ADDTDR/Pitanga/Hardware_Kicad/ltp_kikad_b.png

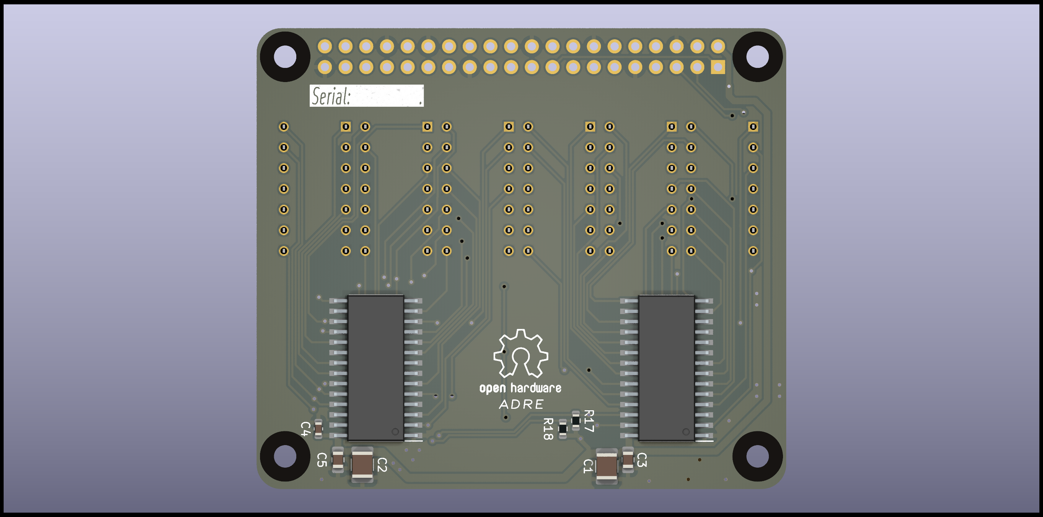
Hardware_Kicad/ltp_kikad_b.png
