ADDTDR/Pitanga/Hardware_Kicad/ltp_kikad_f.png

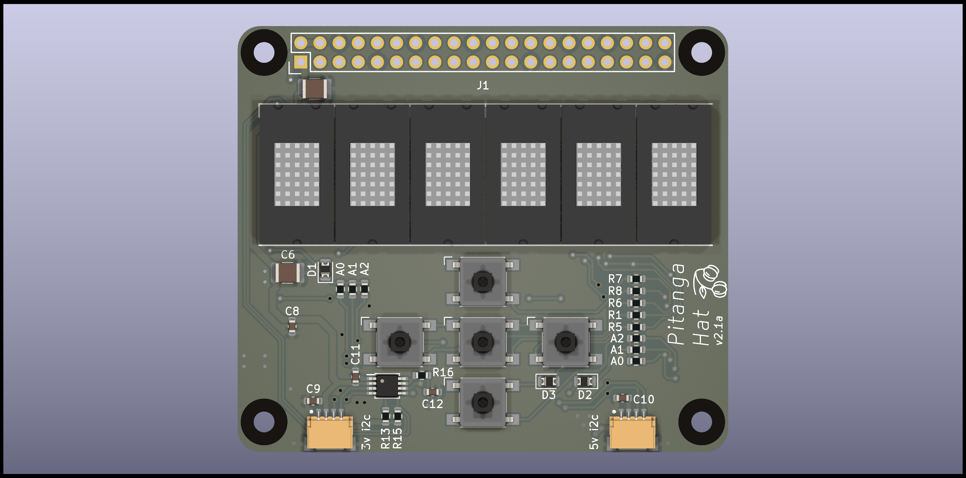
Hardware_Kicad/ltp_kikad_f.png
