ADDTDR/Pitanga/Hardware_Kicad/render_images/ltp_05_f_kikad.png

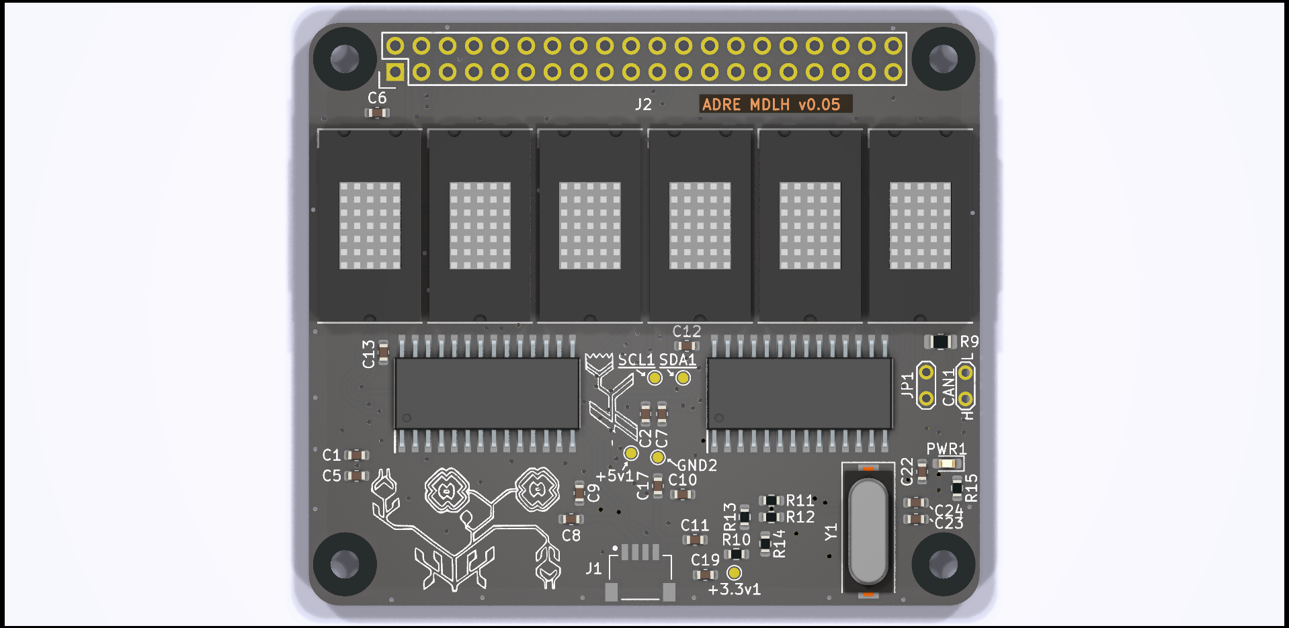
Hardware_Kicad/render_images/ltp_05_f_kikad.png
