ADDTDR/Pitanga/Hardware_Kicad/render_images/ltp_kikad_b7.png

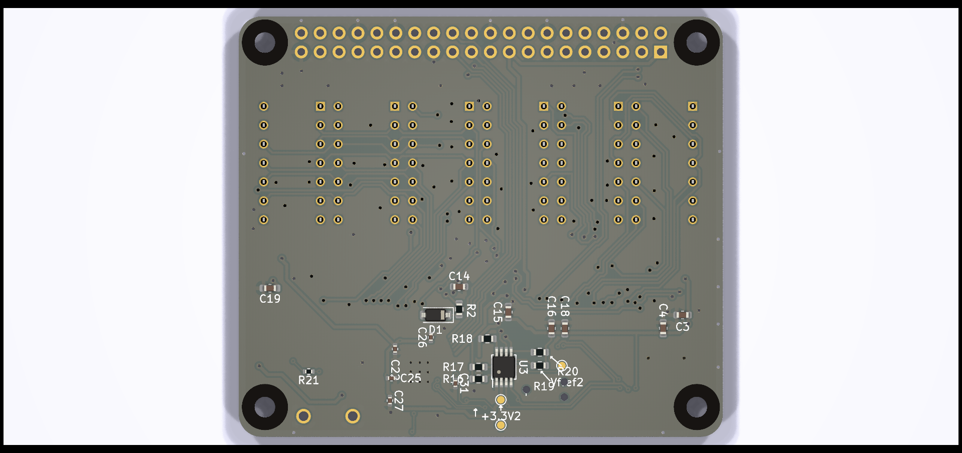
Hardware_Kicad/render_images/ltp_kikad_b7.png
