ADDTDR/Pitanga/Hardware_Kicad/render_images/ltp_kikad_b.png

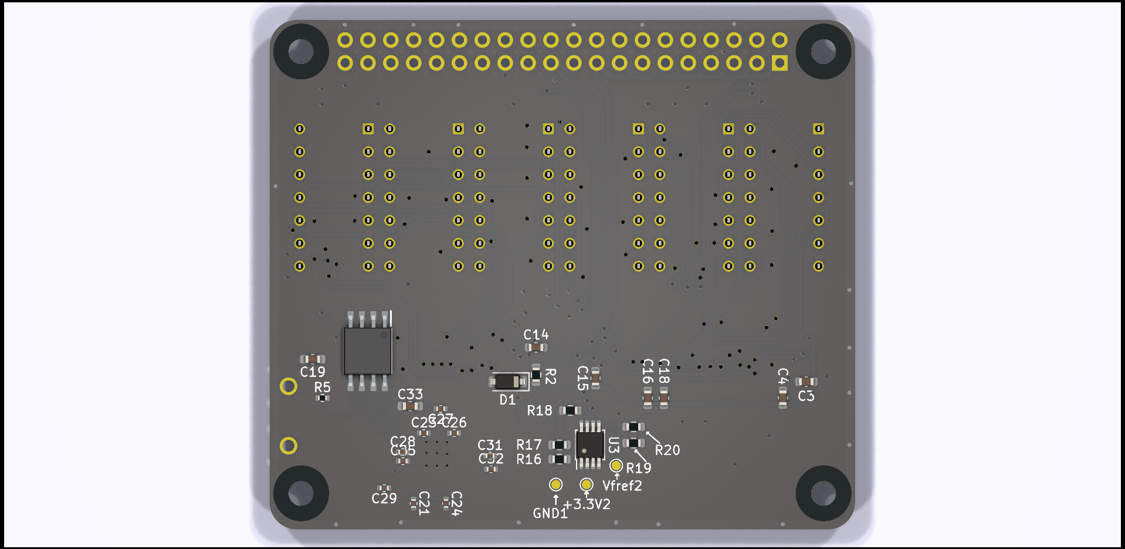
Hardware_Kicad/render_images/ltp_kikad_b.png
