ADDTDR/Pitanga/Hardware_Kicad/render_images/Pitanga 2.1/pitanga_2.1_front.png

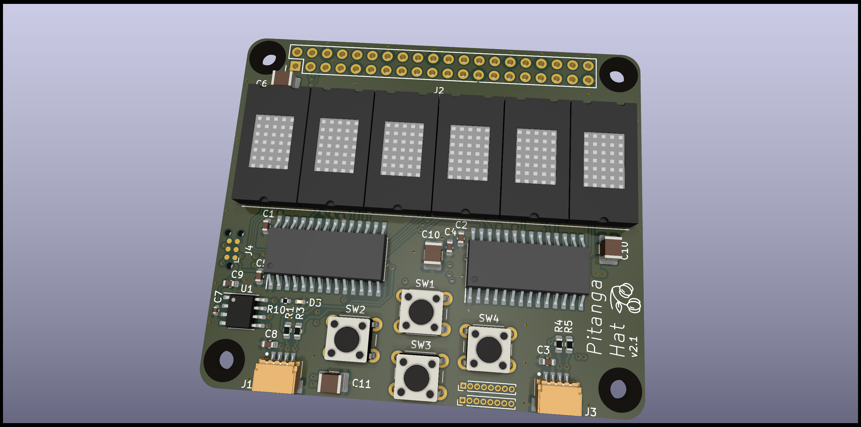
Hardware_Kicad/render_images/Pitanga 2.1/pitanga_2.1_front.png
