ADDTDR/Pitanga/Hardware_Kicad/render_images/Pitanga/pitanga_v2_front.png

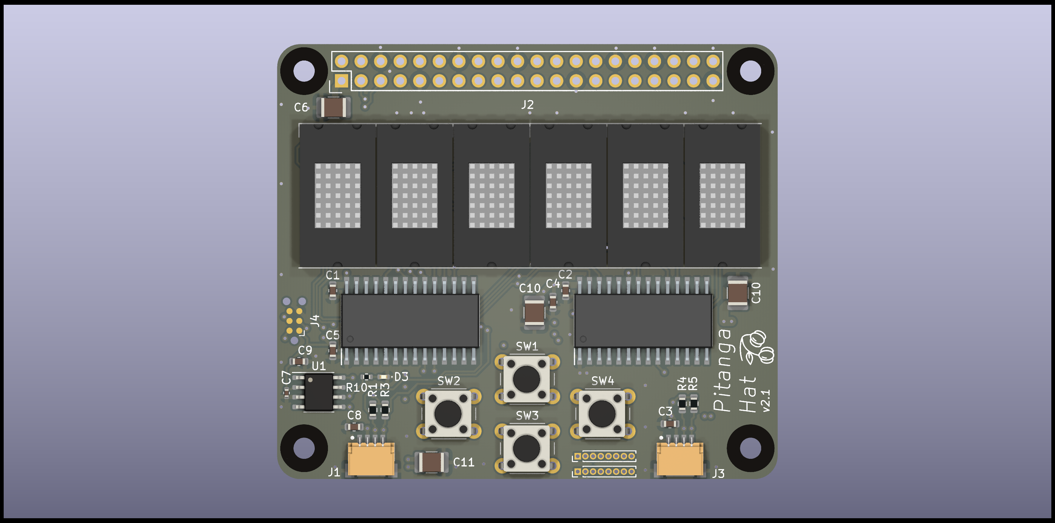
Hardware_Kicad/render_images/Pitanga/pitanga_v2_front.png
