ADDTDR/Pitanga/photo/jpeg/IMG_4408 2.jpeg

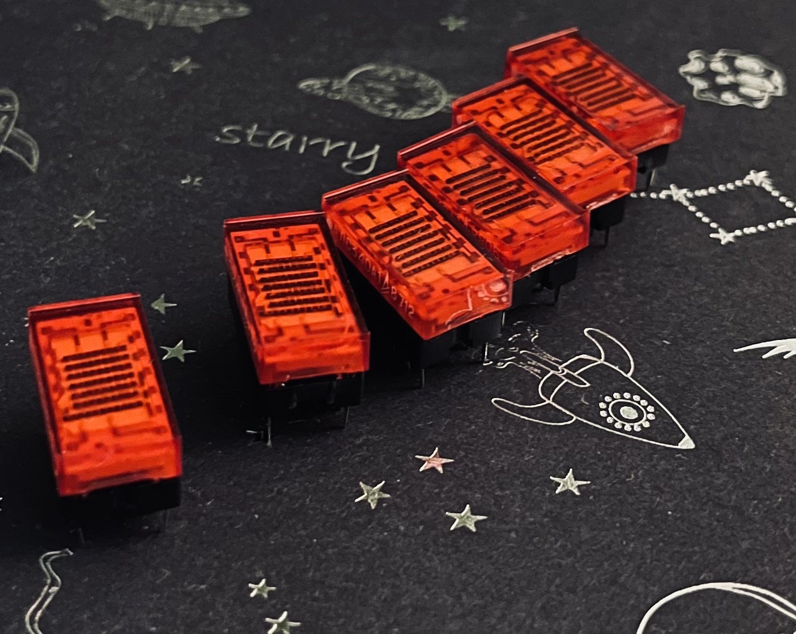
photo/jpeg/IMG_4408 2.jpeg
