ADDTDR/Pitanga/photo/jpeg/IMG_4409 2.jpeg

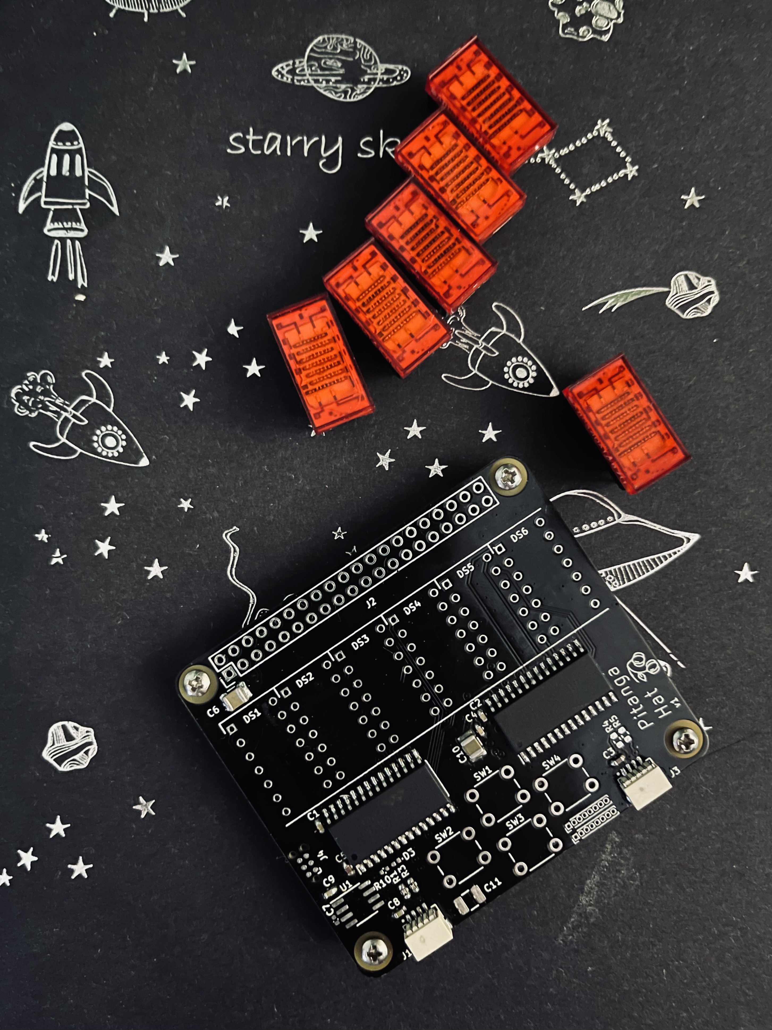
photo/jpeg/IMG_4409 2.jpeg
