ADDTDR/Pitanga/photo/jpeg/IMG_4410 2.jpeg

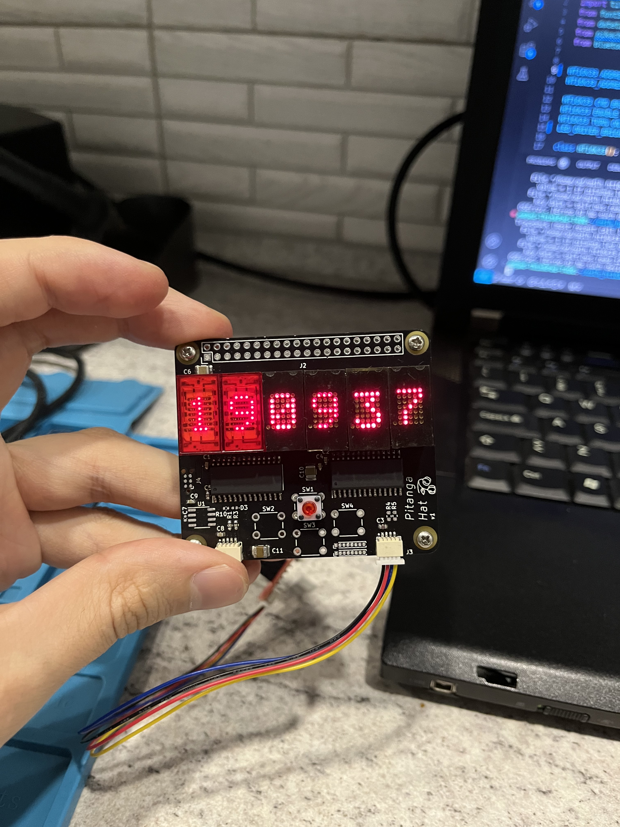
photo/jpeg/IMG_4410 2.jpeg
