ADDTDR/Pitanga/photo/jpeg/IMG_4414 2.jpeg

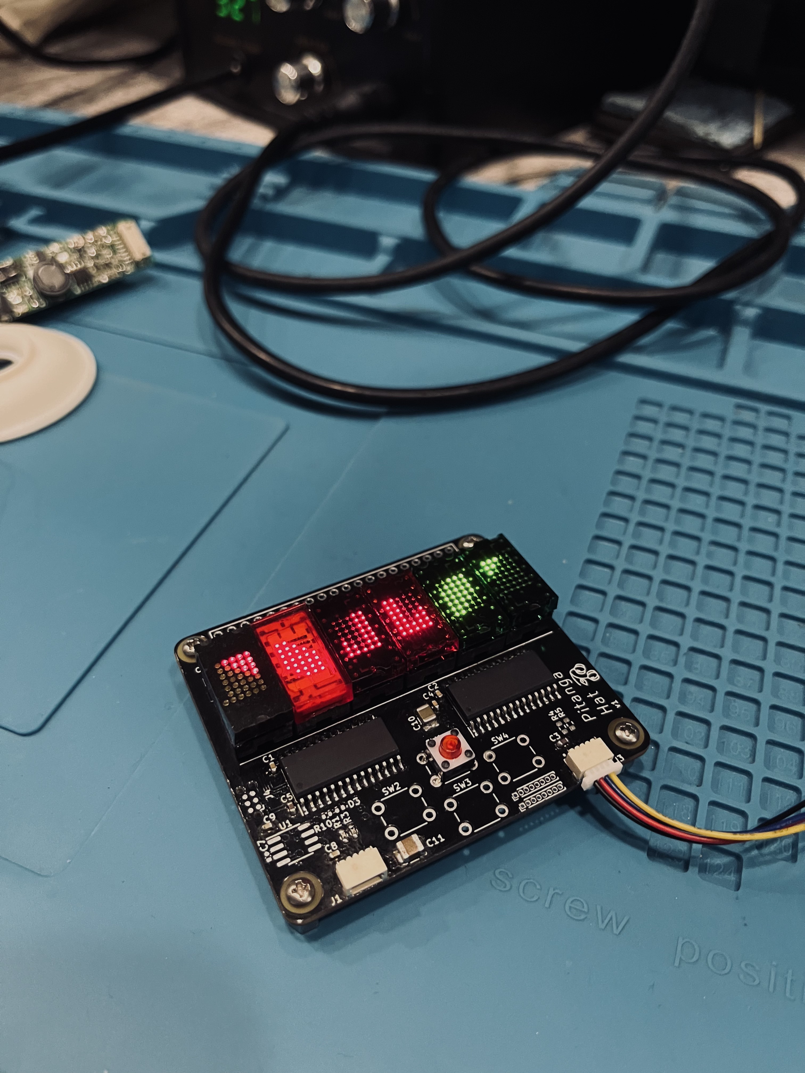
photo/jpeg/IMG_4414 2.jpeg
