ADDTDR/Pitanga/photo/jpeg/IMG_4426 2.jpeg

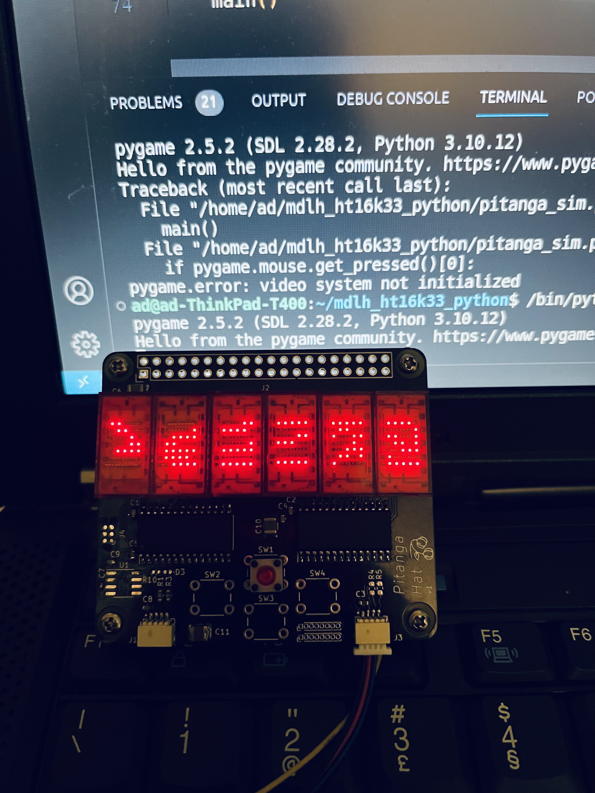
photo/jpeg/IMG_4426 2.jpeg
