ADDTDR/Pitanga/photo/jpeg/IMG_4431 2.jpeg

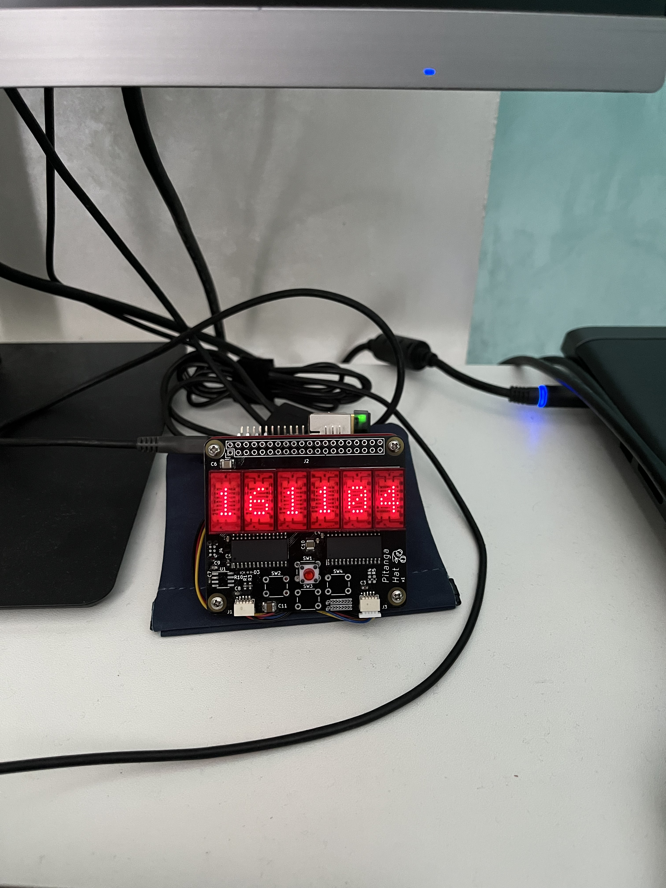
photo/jpeg/IMG_4431 2.jpeg
