ADDTDR/Pitanga/photo/jpeg/photo_5352913656670706159_y.jpeg

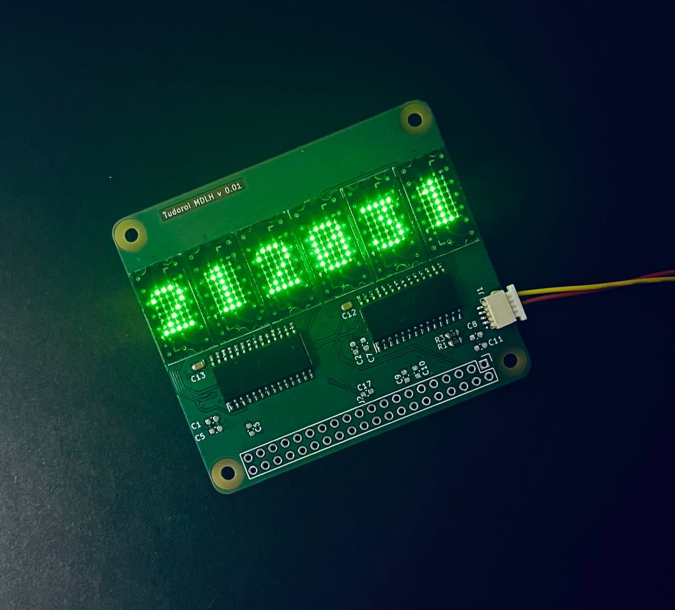
photo/jpeg/photo_5352913656670706159_y.jpeg
